EIT-team/Tanks/Neonate/Meshing/Bodies_For_Meshing_Scalp.STL

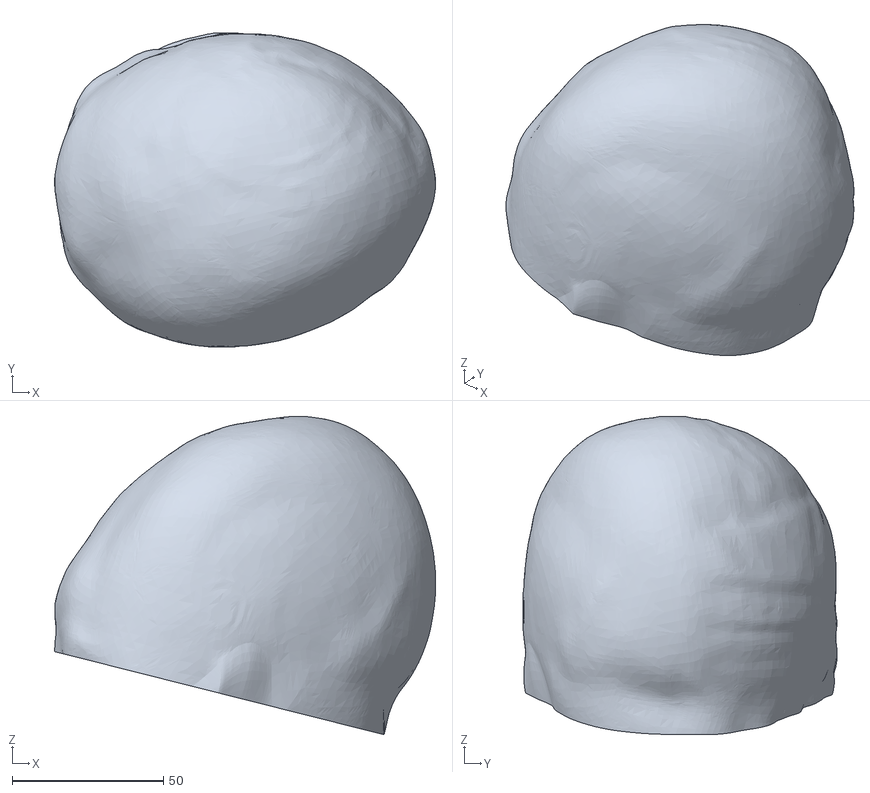
[picture p13: CAD file, 2018-05-30]
Neonate/Meshing/Bodies_For_Meshing_Scalp.STL
125.9 x 103.8 x 105.2
