EIT-team/Tanks/Adult/Meshing/AdultTank_Bodies_For_Meshing-Skull.STL

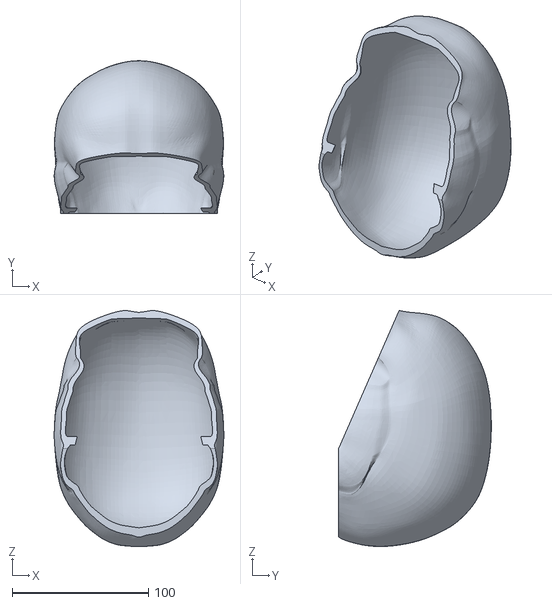
[picture p14: CAD file, 2019-06-07]
Adult/Meshing/AdultTank_Bodies_For_Meshing-Skull.STL
124.3 x 111.9 x 173.0
